cheyao/aniweather/CAD/saber-color.png

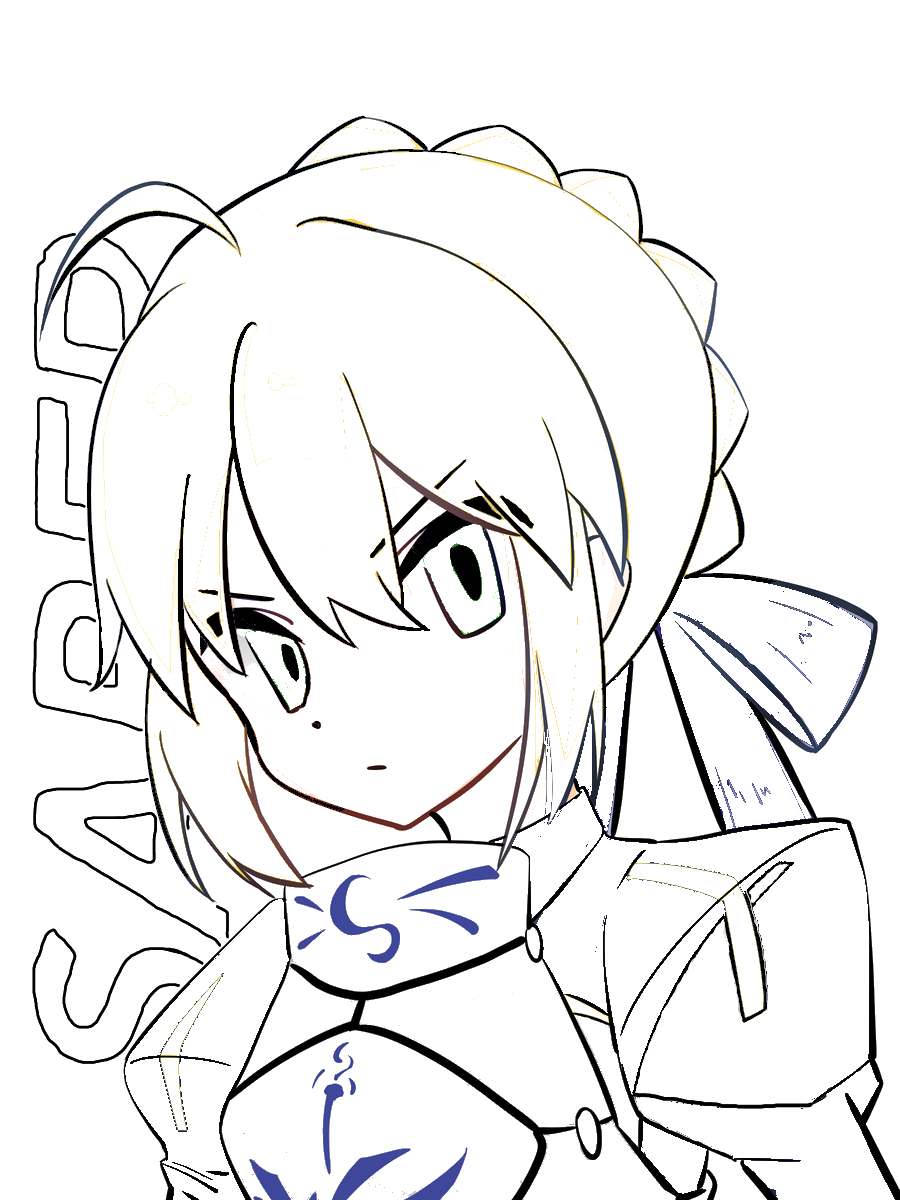
CAD/saber-color.png
